ucb-bar/maveric-bringup/maveric-board-docs/bottom-dfm.png

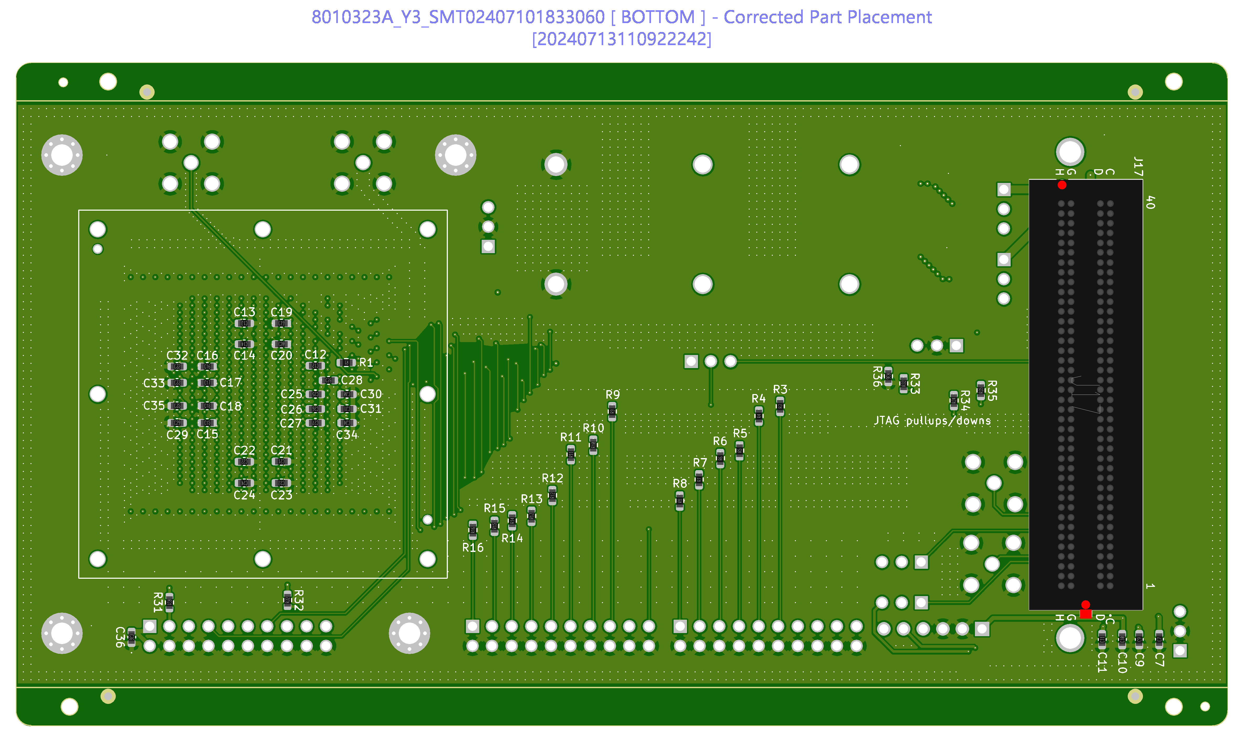
maveric-board-docs/bottom-dfm.png
