ucb-bar/maveric-bringup/maveric-board-docs/bottom-production_file.png

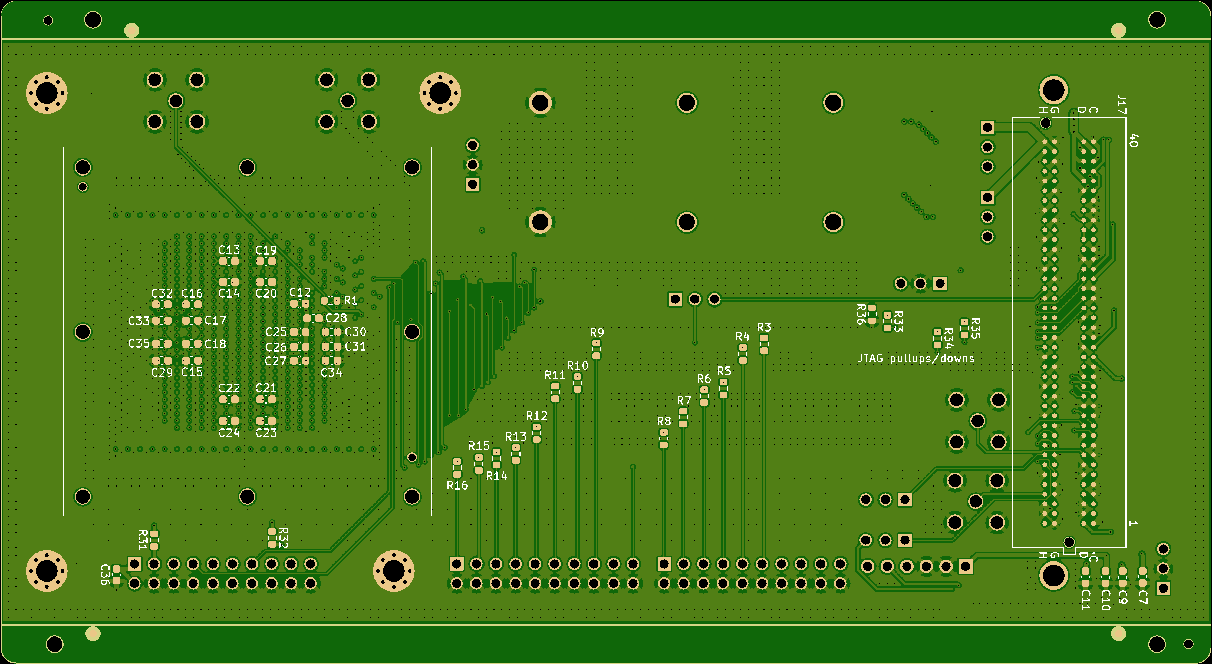
maveric-board-docs/bottom-production_file.png
