ucb-bar/maveric-bringup/maveric-board/07_10_2024-quote/board_3d_view.png

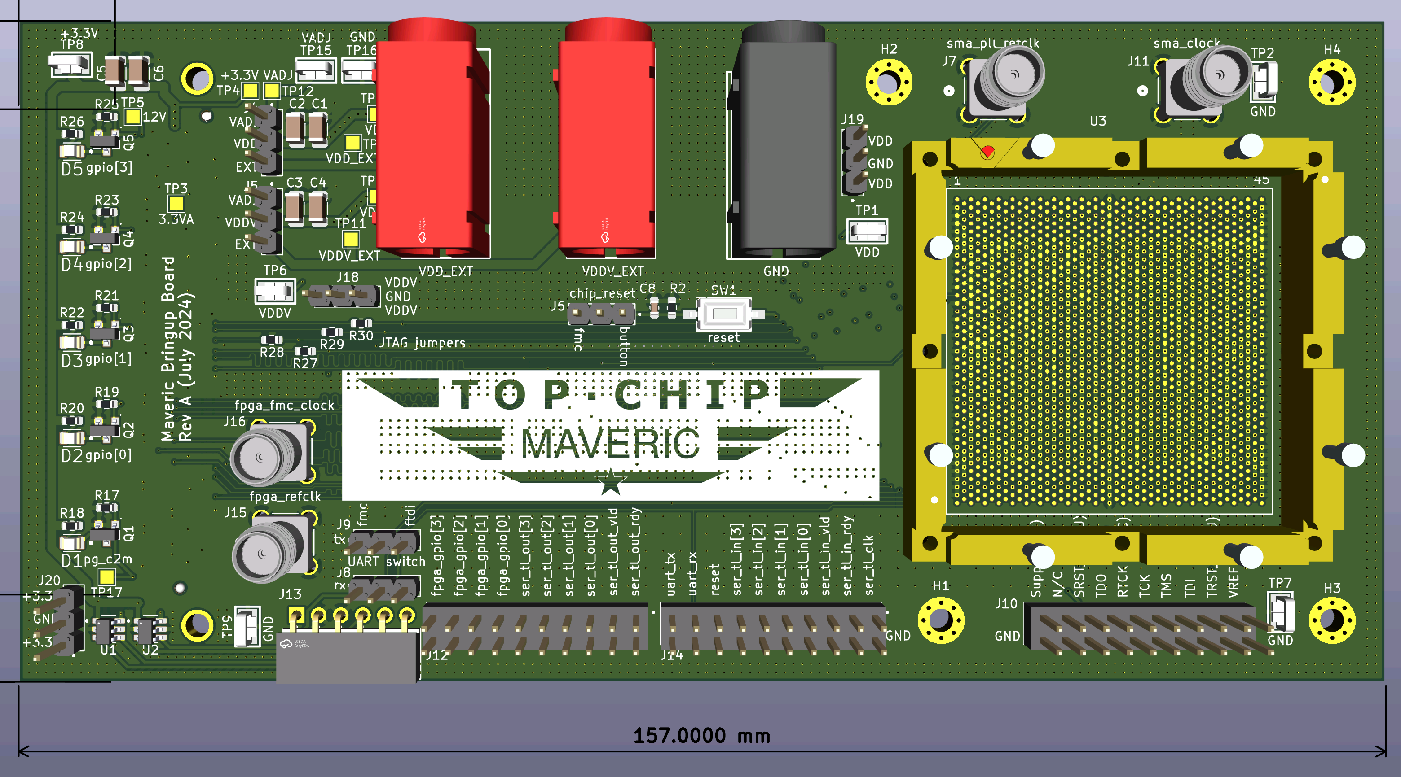
maveric-board/07_10_2024-quote/board_3d_view.png
