ucb-bar/maveric-bringup/maveric-board/07_22_2024-jlcpcb/xray-2.jpg

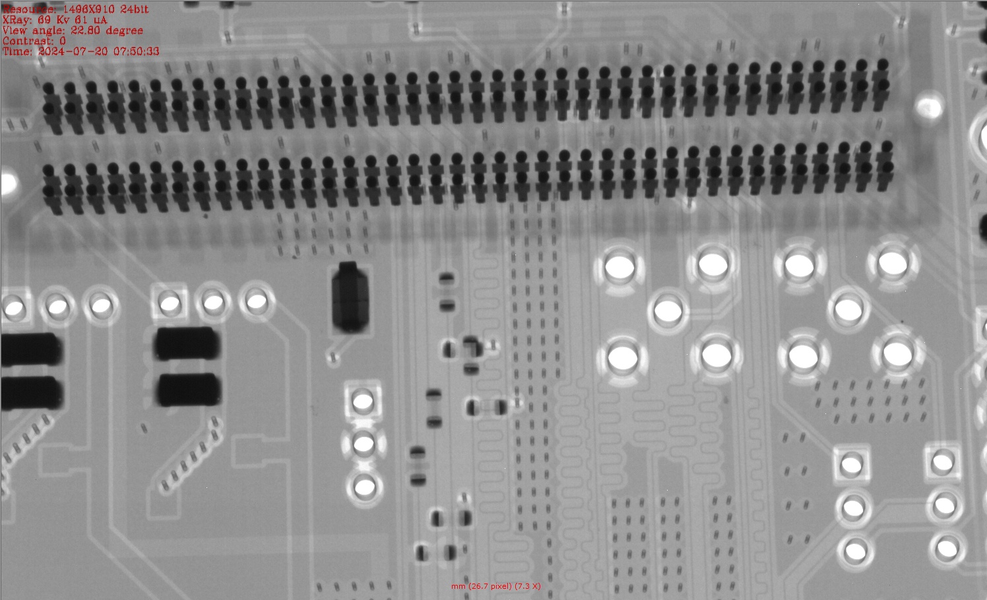
maveric-board/07_22_2024-jlcpcb/xray-2.jpg
