ucb-bar/maveric-bringup/maveric-board/07_10_2024-quote/bom_breakdown.png

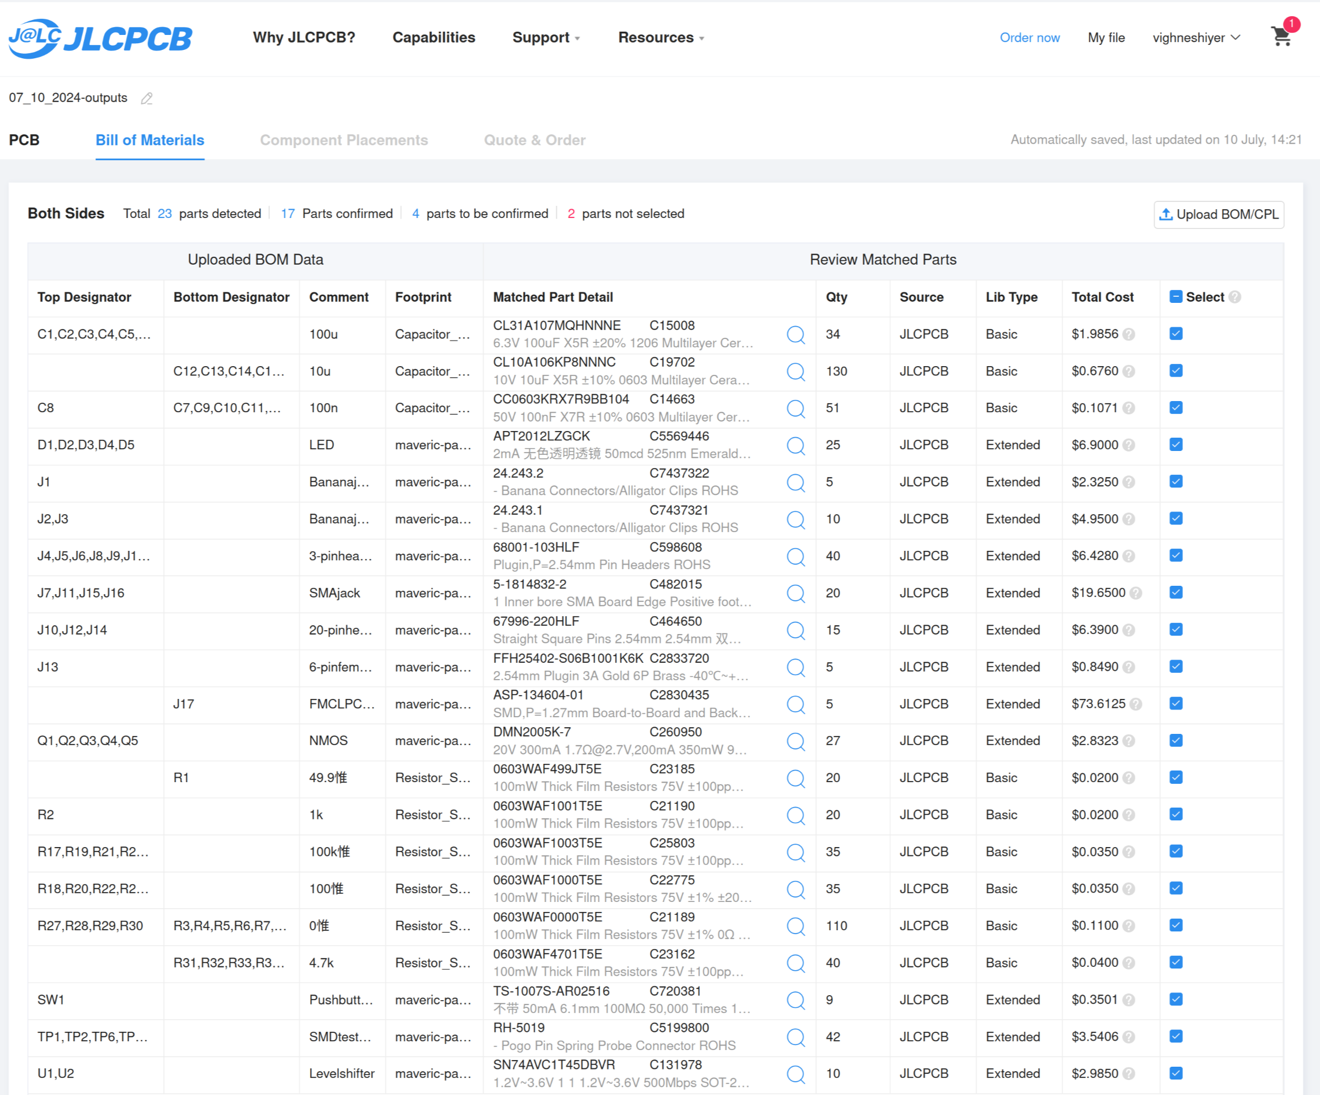
maveric-board/07_10_2024-quote/bom_breakdown.png
